RaffaelloFornasiere/SoundArtProject/Docs/img/photo_2021-05-05_01-32-21.jpg

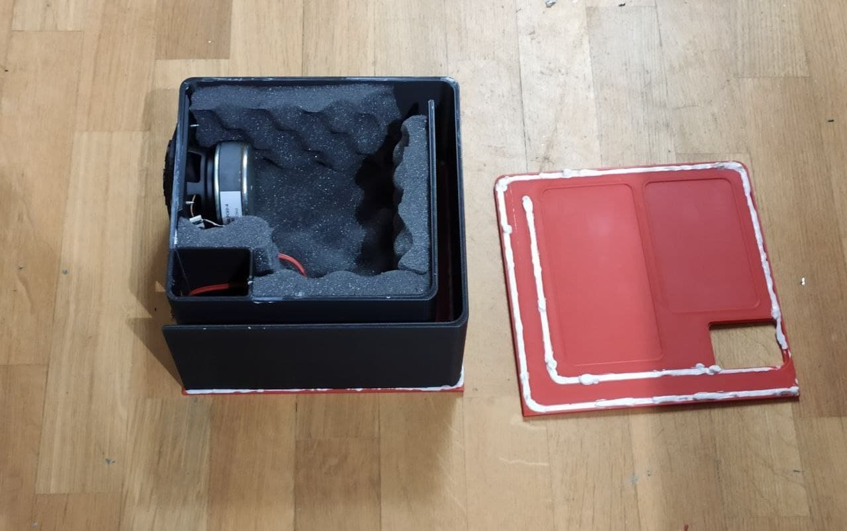
Docs/img/photo_2021-05-05_01-32-21.jpg
