RaffaelloFornasiere/SoundArtProject/Docs/img/photo_2021-05-05_01-32-32.jpg

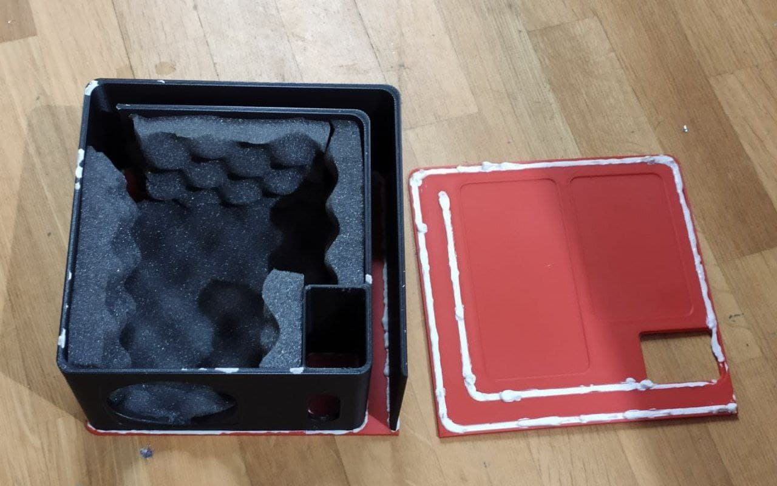
Docs/img/photo_2021-05-05_01-32-32.jpg
