RaffaelloFornasiere/SoundArtProject/Docs/img/photo_2021-05-05_01-32-36.jpg

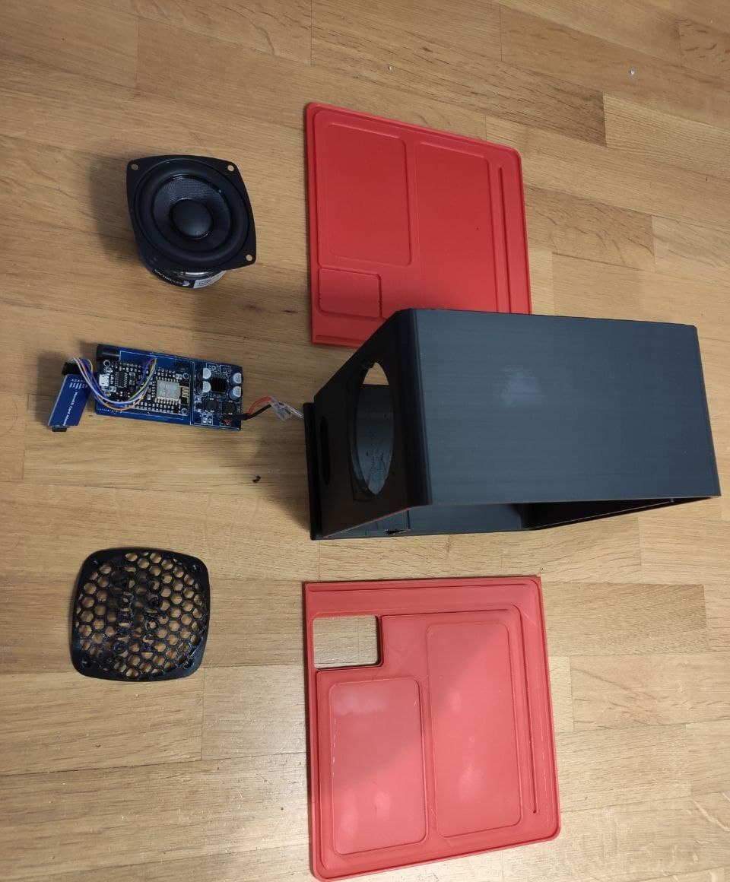
Docs/img/photo_2021-05-05_01-32-36.jpg
