RaffaelloFornasiere/SoundArtProject/Docs/img/photo_2021-05-05_01-32-39.jpg

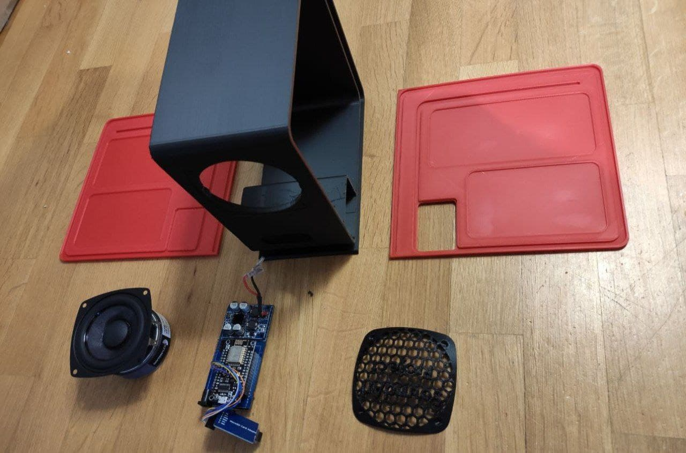
Docs/img/photo_2021-05-05_01-32-39.jpg
