RaffaelloFornasiere/SoundArtProject/Docs/img/photo_2021-05-05_01-32-45.jpg

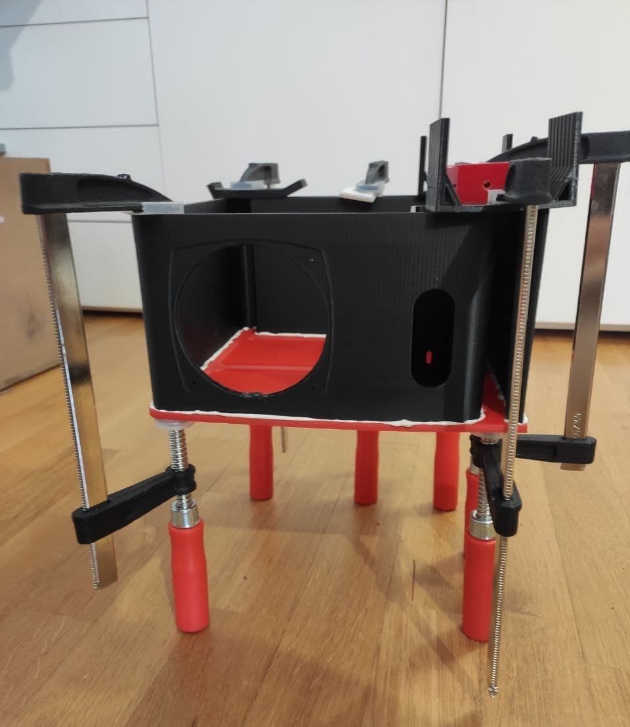
Docs/img/photo_2021-05-05_01-32-45.jpg
