RaffaelloFornasiere/SoundArtProject/Docs/img/photo_2021-05-05_01-32-49.jpg

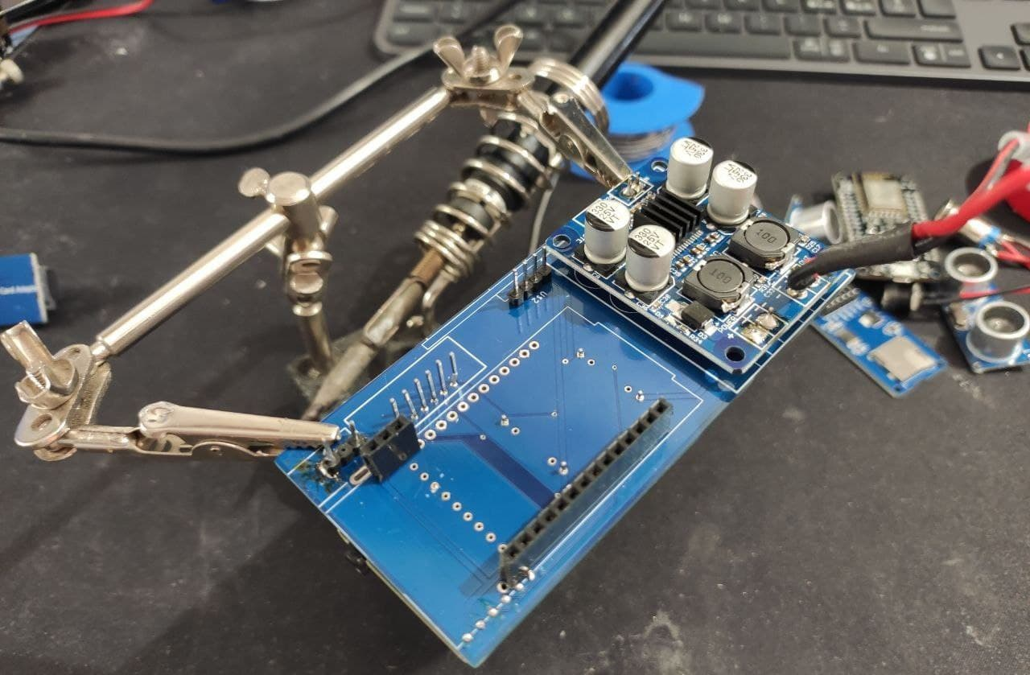
Docs/img/photo_2021-05-05_01-32-49.jpg
