RaffaelloFornasiere/SoundArtProject/Audio/Box/CONECTOR_DC.SLDPRT

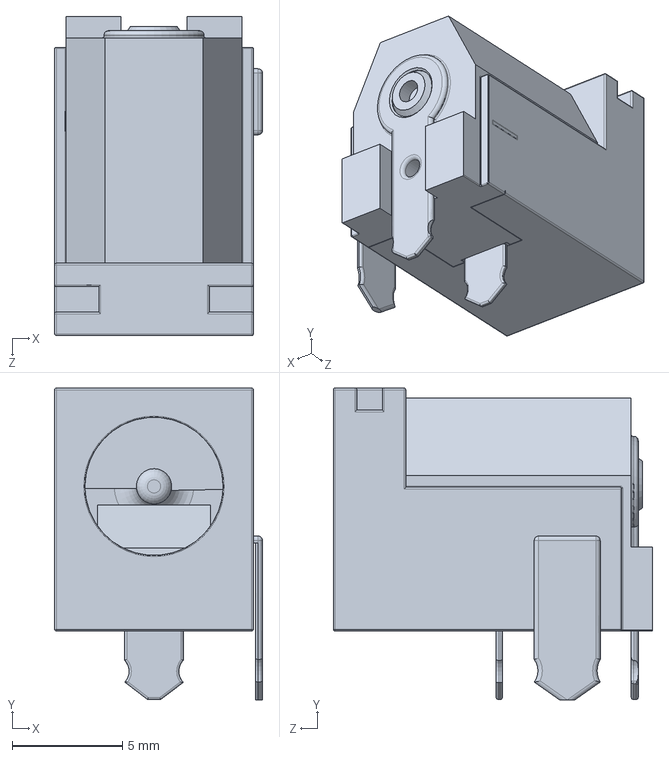
[picture p25: CAD file, 2021-03-16, last stored version]
Audio/Box/CONECTOR_DC.SLDPRT
9.42 x 14.1 x 14.4 mm
