RaffaelloFornasiere/SoundArtProject/Audio/Box/scheda.SLDPRT

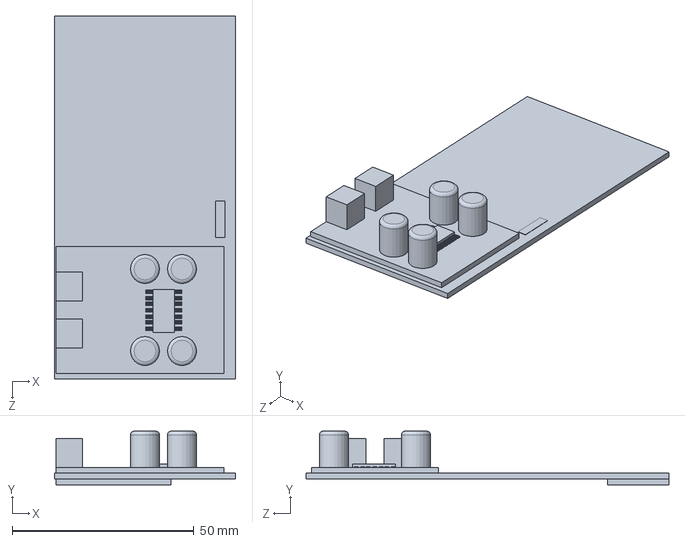
[picture p26: CAD file, 2021-03-16, last stored version]
Audio/Box/scheda.SLDPRT
50.0 x 14.8 x 100.0 mm
