RaffaelloFornasiere/SoundArtProject/EmbeddedCode/Prove/TestSendingFiles/src/main.cpp

#include <ESP8266WiFi.h>
#include <WiFiClient.h>
#include <ESP8266WiFiMulti.h>
#include <ESP8266HTTPClient.h>
#include <ESP8266mDNS.h>
#include <ESP8266WebServer.h>
#include <SD.h>
const char *ssid = "FASTWEB-NGCN3V";
const char *password = "G3P32AOH7L";
ESP8266WiFiMulti wifiMulti; // Create an instance of the ESP8266WiFiMulti class, called 'wifiMulti'

ESP8266WebServer server(80); // Create a webserver object that listens for HTTP request on port 80



String getContentType(String filename); // convert the file extension to the MIME type
bool handleFileRead(String path);       // send the right file to the client (if it exists)
void handleFileUpload();                // upload a new file to the SD
void setup()
{
    
    //client.begin()

    Serial.begin(115200); // Start the Serial communication to send messages to the computer
    delay(10);
    Serial.println('\n');

    wifiMulti.addAP(ssid, password); // add Wi-Fi networks you want to connect to

    Serial.println("Connecting ...");
    int i = 0;
    while (wifiMulti.run() != WL_CONNECTED)
    { // Wait for the Wi-Fi to connect
        delay(1000);
        Serial.print(++i);
        Serial.print(' ');
    }
    Serial.println('\n');
    Serial.print("Connected to ");
    Serial.println(WiFi.SSID()); // Tell us what network we're connected to
    Serial.print("IP address:\t");
    Serial.println(WiFi.localIP()); // Send the IP address of the ESP8266 to the computer

    if (MDNS.begin("esp8266"))
    { // Start the mDNS responder for esp8266.local
        Serial.println("mDNS responder started");
    }
    else
    {
        Serial.println("Error setting up MDNS responder!");
    }

    SD.begin(D2); // Start the SPI Flash Files System

    server.on("/upload", HTTP_GET, []() {                 // if the client requests the upload page
    if (!handleFileRead("/upload.html"))                // send it if it exists
      server.send(404, "text/plain", "404: Not Found"); // otherwise, respond with a 404 (Not Found) error
  });
    

    server.on(
        "/upload/uri", HTTP_POST, // if the client posts to the upload page
        []() { server.send(200); },
        handleFileUpload // Receive and save the file
    );

    server.onNotFound([]() {                                  // If the client requests any URI
        if (!handleFileRead(server.uri()))                    // send it if it exists
            server.send(404, "text/plain", "404: Not Found"); // otherwise, respond with a 404 (Not Found) error
    });

    server.begin(); // Actually start the server
    Serial.println("HTTP server started");
}

void loop()
{
    server.handleClient();
}


String getContentType(String filename){
  if(filename.endsWith(".htm")) return "text/html";
  else if(filename.endsWith(".html")) return "text/html";
  else if(filename.endsWith(".css")) return "text/css";
  else if(filename.endsWith(".js")) return "application/javascript";
  else if(filename.endsWith(".png")) return "image/png";
  else if(filename.endsWith(".gif")) return "image/gif";
  else if(filename.endsWith(".jpg")) return "image/jpeg";
  else if(filename.endsWith(".ico")) return "image/x-icon";
  else if(filename.endsWith(".xml")) return "text/xml";
  else if(filename.endsWith(".pdf")) return "application/x-pdf";
  else if(filename.endsWith(".zip")) return "application/x-zip";
  else if(filename.endsWith(".gz")) return "application/x-gzip";
  return "text/plain";
}


bool handleFileRead(String path)
{ // send the right file to the client (if it exists)
    Serial.println("handleFileRead: " + path);
    if (path.endsWith("/"))
        path += "indexU.html";                  // If a folder is requested, send the index file
    String contentType = getContentType(path); // Get the MIME type
    String pathWithGz = path + ".gz";
    if (SD.exists(pathWithGz) || SD.exists(path))
    {                                                       // If the file exists, either as a compressed archive, or normal
        if (SD.exists(pathWithGz))                      // If there's a compressed version available
            path = pathWithGz;                              // Use the compressed verion
        File file = SD.open(path, "r");                 // Open the file
        size_t sent = server.streamFile(file, contentType); // Send it to the client
        file.close();                                       // Close the file again
        Serial.println(String("\tSent file: ") + path);
        return true;
    }
    Serial.println(String("\tFile Not Found: ") + path); // If the file doesn't exist, return false
    return false;
}


void handleFileUpload()
{ // upload a new file to the SD
    static File fsUploadFile;
    HTTPUpload &upload = server.upload();
 
    if (upload.status == UPLOAD_FILE_START)
    {
        String filename = upload.filename;
        if (!filename.startsWith("/"))
            filename = "/" + filename;
        Serial.print("handleFileUpload Name: ");
        Serial.println(filename);
        fsUploadFile = SD.open(filename, "w"); // Open the file for writing in SD (create if it doesn't exist)
    }
    else if (upload.status == UPLOAD_FILE_WRITE)
    {
        if (fsUploadFile)
            fsUploadFile.write(upload.buf, upload.currentSize); // Write the received bytes to the file
    }
    else if (upload.status == UPLOAD_FILE_END)
    {
        if (fsUploadFile)
        {                         // If the file was successfully created
            fsUploadFile.close(); // Close the file again
            Serial.print("handleFileUpload Size: ");
            Serial.println(upload.totalSize);
            server.sendHeader("Location", "/success.html"); // Redirect the client to the success page
            server.send(303);
        }
        else
        {
            Serial.println("File upload failed");
            server.send(500, "text/plain", "500: couldn't create file");
        }
    }
}
